sschwaab/aes-dac/hw/sim/DeltaSigma-OutputFilter.asc

C1: cap; 680p
C2: cap; 680p
C3: cap; 3300p
C4: cap; 10µ
C5: cap; 10µ
R1: res; 360
R2: res; 360
R3: res; 470
R4: res; 10k
R5: res; 7.5k
R6: res; 7.5k
R9: res; 5.6k
R10: res; 5.6k
U1: ADA4510
V1: voltage; SINE(0 2 440); AC 1 0
V2: voltage; 5
V3: voltage; SINE(0 2 440 0 0 180); AC 1 180
V4: voltage; -5
Named nets: 0, V+, V-
.tran 100m
.ac dec 1000 10 1Meg
