sschwaab/aes-dac/hw/sim/MFB.asc

11k: res; 16k
C1: cap; 900p
C2: cap; 225p
C3: cap; 225p
C4: cap; 900p
C5: cap; 10µ
C6: cap; 10µ
C7: cap; 220p
C8: cap; 680p
C9: cap; 220p
C10: cap; 680p
C11: cap; 10µ
C12: cap; 10µ
R1: res; 5k
R2: res; 5k
R3: res; 220
R4: res; 10k
R5: res; 220
R6: res; 10k
R7: res; 10k
R8: res; 10k
R9: res; 10k
R10: res; 10k
R12: res; 220
R13: res; 1Meg
R14: res; 8200
R15: res; 3.6k
R16: res; 16k
R17: res; 220
R18: res; 1Meg
R19: res; 8200
R20: res; 3.6k
U1: ADA4510
U2: ADA4510
U3: ADA4510
U4: ADA4510
V1: voltage; SINE(2.5 2 440); AC 1 0
V2: voltage; 9
V3: voltage; 2.5
V4: voltage; -9
V5: voltage; SINE(2.5 2 440 0 0 180); AC 1 180
V6: voltage; 2.5
V7: voltage; SINE(2.5 2 440); AC 1 0
V8: voltage; 2.5
V9: voltage; SINE(2.5 2 440 0 0 180); AC 1 180
V10: voltage; 2.5
Named nets: 0, V+, V-, IN+, IN-, OUT-, OUT+
.tran 10m
.ac dec 1000 10 1Meg
