sschwaab/aes-dac/hw/sim/MFB_OPA1612.asc

11k: res; {R2}
C1: cap; {C1}
C2: cap; {C2}
C3: cap; {C2}
C4: cap; {C1}
C5: cap; {Cout}
C6: cap; {Cout}
C7: cap; {C2}
C8: cap; {C1}
C9: cap; {C2}
C10: cap; {C1}
C11: cap; {Cout}
C12: cap; {Cout}
R1: res; {R2}
R2: res; {R2}
R3: res; 100
R4: res; {Rload}
R5: res; 100
R6: res; {R1}
R7: res; {Rload}
R8: res; {R3}
R9: res; {R1}
R10: res; {R3}
R12: res; 100
R13: res; {Rload}
R14: res; {R1}
R15: res; {R3}
R16: res; {R2}
R17: res; 100
R18: res; {Rload}
R19: res; {R1}
R20: res; {R3}
U1: OPA161x
U2: OPA161x
U3: OPA161x
U5: OPA161x
V1: voltage; SINE(2.5 2 440); AC 1 0
V2: voltage; 9
V3: voltage; 2.5
V4: voltage; 0
V5: voltage; SINE(2.5 2 440 0 0 180); AC 1 180
V6: voltage; 2.5
V7: voltage; SINE(2.5 2 440); AC 1 0
V8: voltage; 2.5
V9: voltage; SINE(2.5 2 440 0 0 180); AC 1 180
V10: voltage; 2.5
Named nets: 0, V+, V-, IN+, IN-, OUT-, OUT+
.tran 10m
.ac dec 1000 10 1Meg
.param R1=8.2k R2=16k R3=3.6k C1=680p C2=220p Cout=33u Rload=10k
step param Rload 1k 20k 3k
1.24VRMS
 
1.23VRMS = 4dBu
1.37VRMS = 5 dBu
