sschwaab/aes-dac/hw/sim/SplitRail.asc

C1: cap; 1n
C2: cap; 100n
C3: cap; 10µ
C4: cap; 10µ
Q1: npn; BC547C
Q2: pnp; BC857C
R1: res; 10k
R2: res; 10k
R3: res; 100k
R4: res; 100
R5: res; 10k
R6: res; 10k
U1: ADA4510
V1: voltage; 9
Named nets: 0, v+, v-, FB
.tran 100m
